coolvnod/palm-scan/hardware/kicad/buzzer.kicad_sch

## KiCad design hardware/kicad/buzzer.kicad_sch (2026-09-14)

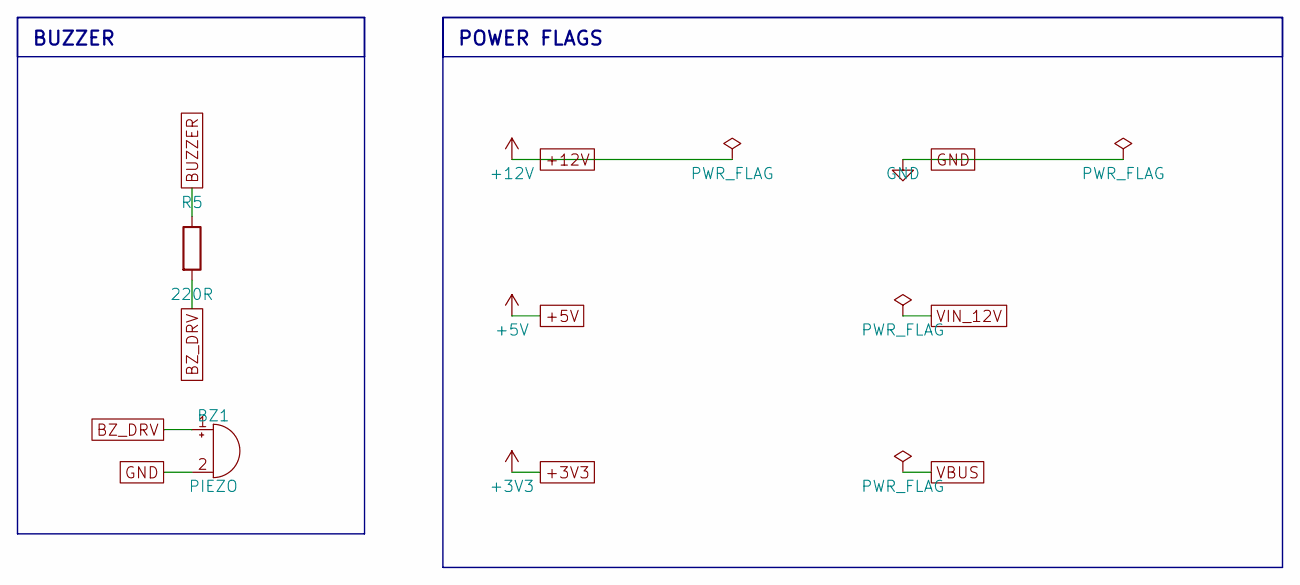
[picture p36: schematic buzzer.kicad_sch]

Parts:
BZ1: PIEZO; Buzzer_12x9.5RM7.6
R5: 220R; R_0603_1608Metric

Connections:
BUZZER: R5.1
BZ_DRV: BZ1.1 (+), R5.2
GND: BZ1.2 (-)

Notes on the sheet:
BUZZER
POWER FLAGS
