coolvnod/palm-scan/hardware/kicad/display.kicad_sch

## KiCad design hardware/kicad/display.kicad_sch (2026-09-14)

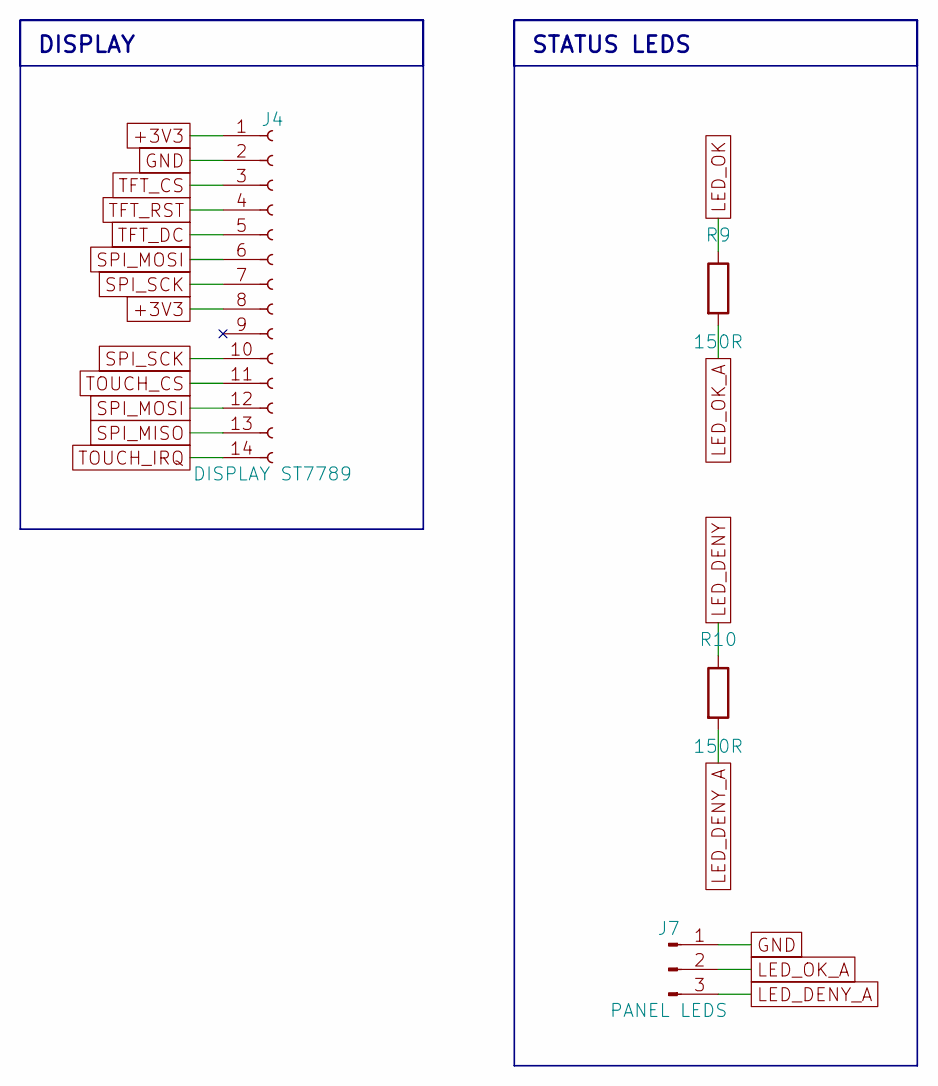
[picture p37: schematic display.kicad_sch]

Parts:
J4: DISPLAY ST7789; PinSocket_1x14_P2.54mm_Vertical
J7: PANEL LEDS; PinHeader_1x03_P2.54mm_Vertical
R9, R10: 150R; R_0603_1608Metric

Connections:
+3V3: J4.1, J4.8
GND: J4.2, J7.1
LED_DENY: R10.1
LED_DENY_A: J7.3, R10.2
LED_OK: R9.1
LED_OK_A: J7.2, R9.2
SPI_MISO: J4.13
SPI_MOSI: J4.6, J4.12
SPI_SCK: J4.7, J4.10
TFT_CS: J4.3
TFT_DC: J4.5
TFT_RST: J4.4
TOUCH_CS: J4.11
TOUCH_IRQ: J4.14

Notes on the sheet:
DISPLAY
STATUS LEDS
