coolvnod/palm-scan/hardware/kicad/exit.kicad_sch

## KiCad design hardware/kicad/exit.kicad_sch (2026-09-14)

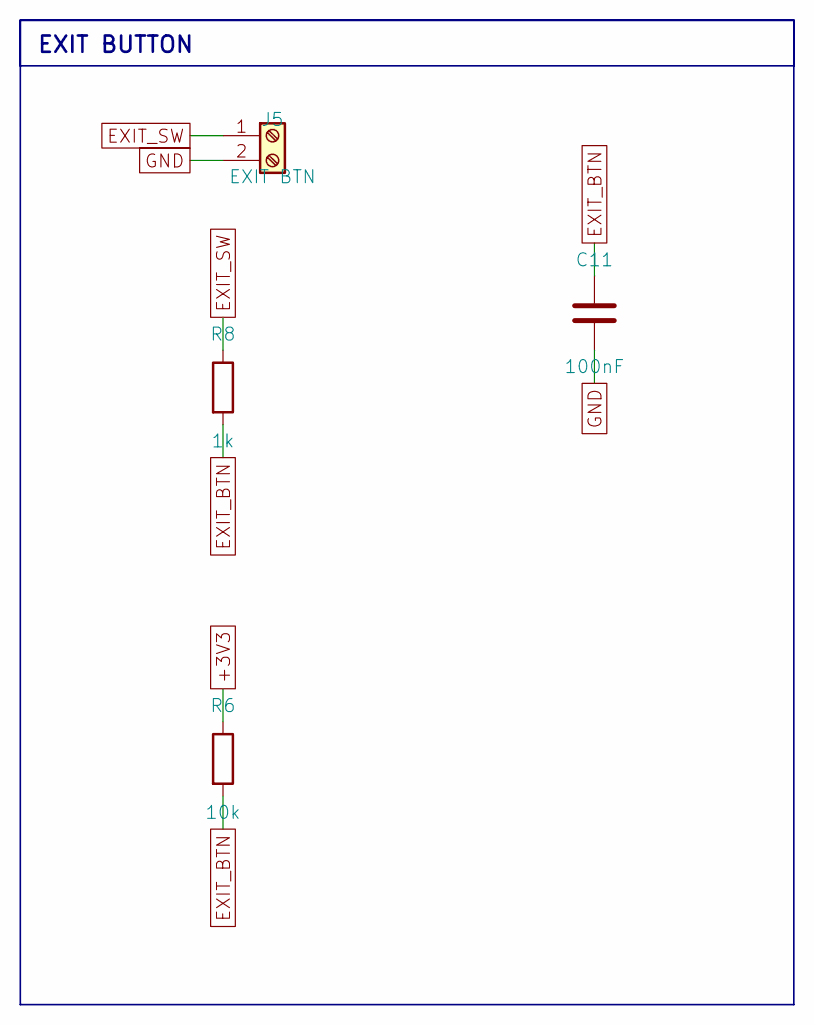
[picture p38: schematic exit.kicad_sch]

Parts:
C11: 100nF; C_0603_1608Metric
J5: EXIT BTN; TerminalBlock_Phoenix_MKDS-1,5-2-5.08_1x02_P5.08mm_Horizont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
R6: 10k; R_0603_1608Metric
R8: 1k; R_0603_1608Metric

Connections:
+3V3: R6.1
EXIT_BTN: C11.1, R6.2, R8.2
EXIT_SW: J5.1, R8.1
GND: C11.2, J5.2

Notes on the sheet:
EXIT BUTTON
