coolvnod/palm-scan/hardware/kicad/lock.kicad_sch

## KiCad design hardware/kicad/lock.kicad_sch (2026-09-14)

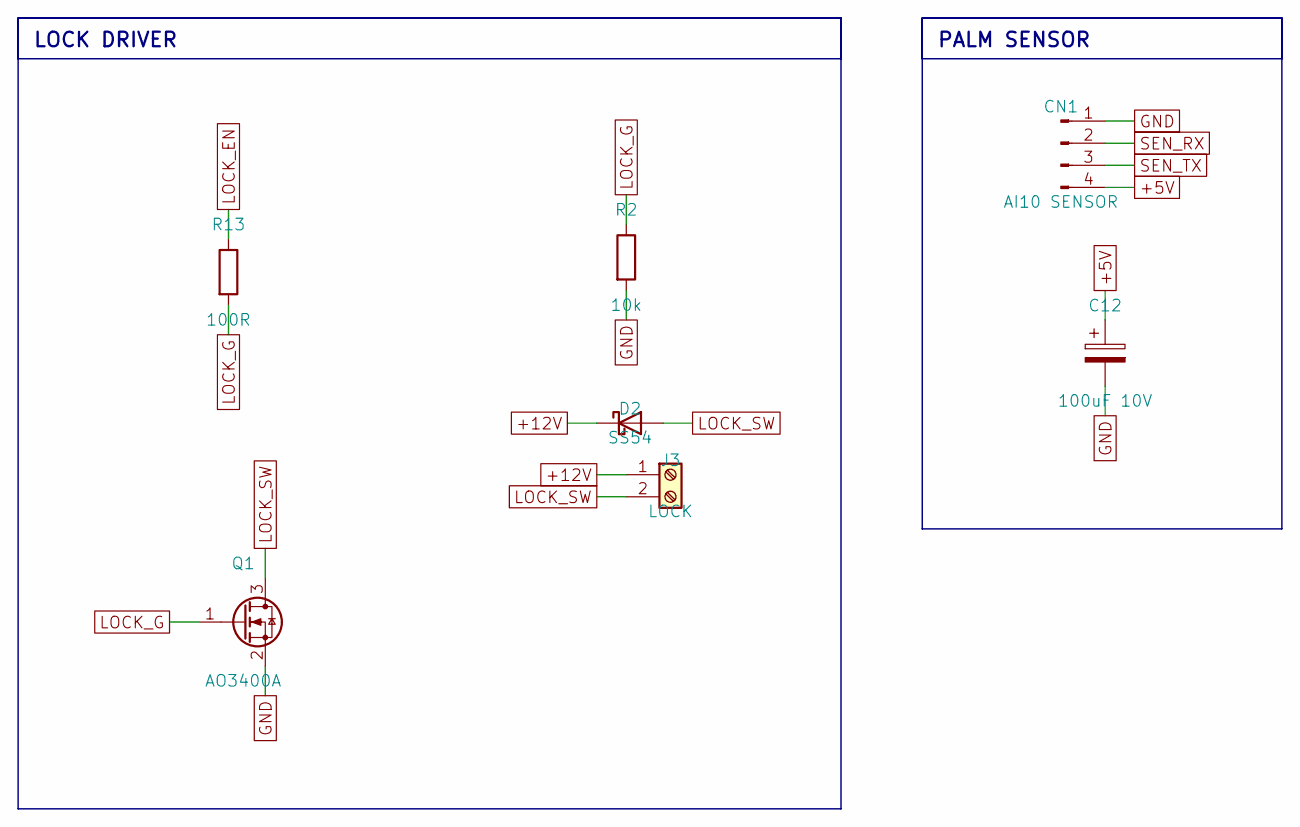
[picture p39: schematic lock.kicad_sch]

Parts:
C12: 100uF 10V; CP_Elec_6.3x5.4
CN1: AI10 SENSOR; Molex_PicoBlade_53047-0410_1x04_P1.25mm_Vertical
D2: SS54; D_SMA
J3: LOCK; TerminalBlock_Phoenix_MKDS-1,5-2-5.08_1x02_P5.08mm_Horizont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
Q1: AO3400A; SOT-23
R2: 10k; R_0603_1608Metric
R13: 100R; R_0603_1608Metric

Connections:
+5V: C12.1, CN1.4
+12V: D2.1 (K), J3.1
GND: C12.2, CN1.1, Q1.2 (S), R2.2
LOCK_EN: R13.1
LOCK_G: Q1.1 (G), R2.1, R13.2
LOCK_SW: D2.2 (A), J3.2, Q1.3 (D)
SEN_RX: CN1.2
SEN_TX: CN1.3

Notes on the sheet:
LOCK DRIVER
PALM SENSOR
