coolvnod/palm-scan/hardware/kicad/mcu.kicad_sch

## KiCad design hardware/kicad/mcu.kicad_sch (2026-09-14)

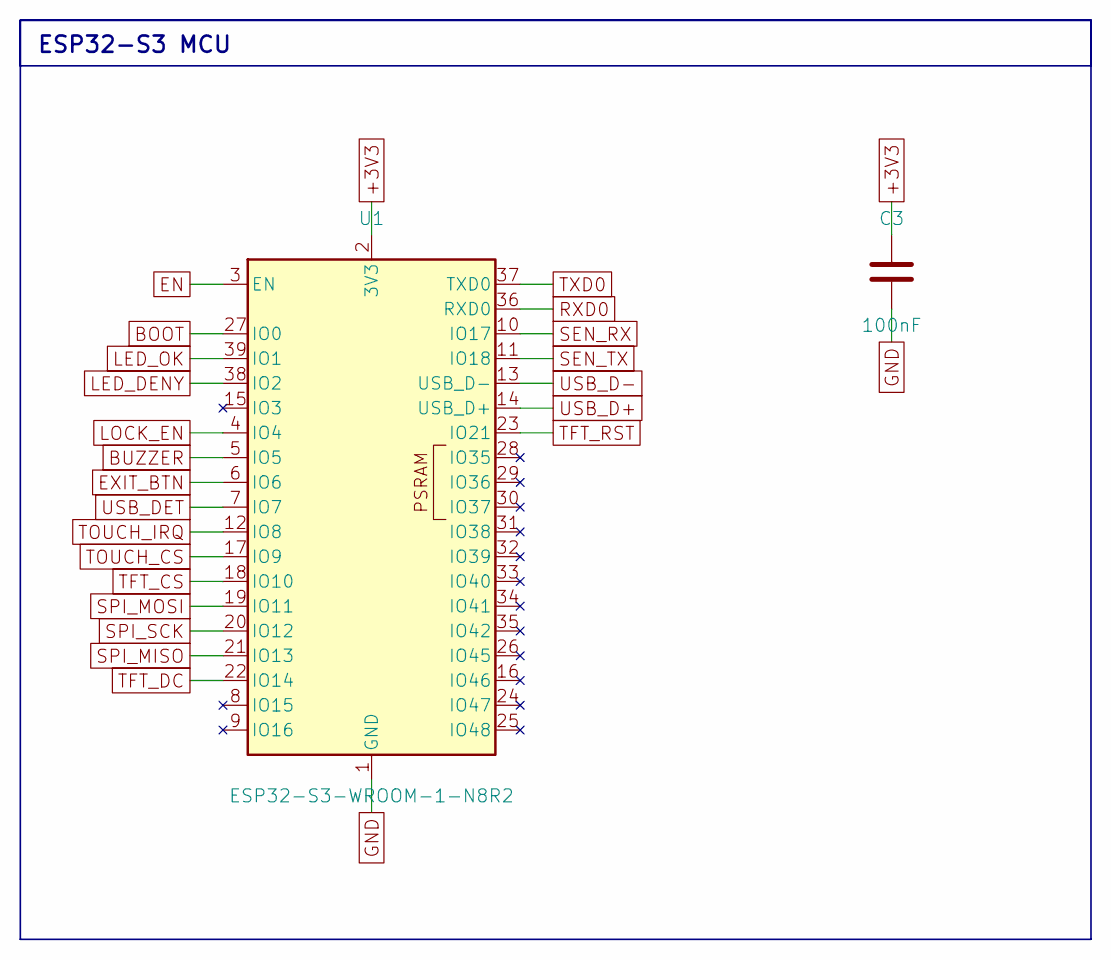
[picture p40: schematic mcu.kicad_sch]

Parts:
C3: 100nF; C_0603_1608Metric
U1: ESP32-S3-WROOM-1-N8R2; ESP32-S3-WROOM-1

Connections:
+3V3: C3.1, U1.2 (3V3)
BOOT: U1.27 (IO0)
BUZZER: U1.5 (IO5)
EN: U1.3 (EN)
EXIT_BTN: U1.6 (IO6)
GND: C3.2, U1.1 (GND), U1.40 (GND), U1.41 (GND)
LED_DENY: U1.38 (IO2)
LED_OK: U1.39 (IO1)
LOCK_EN: U1.4 (IO4)
RXD0: U1.36 (RXD0)
SEN_RX: U1.10 (IO17)
SEN_TX: U1.11 (IO18)
SPI_MISO: U1.21 (IO13)
SPI_MOSI: U1.19 (IO11)
SPI_SCK: U1.20 (IO12)
TFT_CS: U1.18 (IO10)
TFT_DC: U1.22 (IO14)
TFT_RST: U1.23 (IO21)
TOUCH_CS: U1.17 (IO9)
TOUCH_IRQ: U1.12 (IO8)
TXD0: U1.37 (TXD0)
USB_D+: U1.14 (USB_D+)
USB_D-: U1.13 (USB_D-)
USB_DET: U1.7 (IO7)

Notes on the sheet:
ESP32-S3 MCU
