coolvnod/palm-scan/hardware/kicad/power_in.kicad_sch

## KiCad design hardware/kicad/power_in.kicad_sch (2026-09-14)

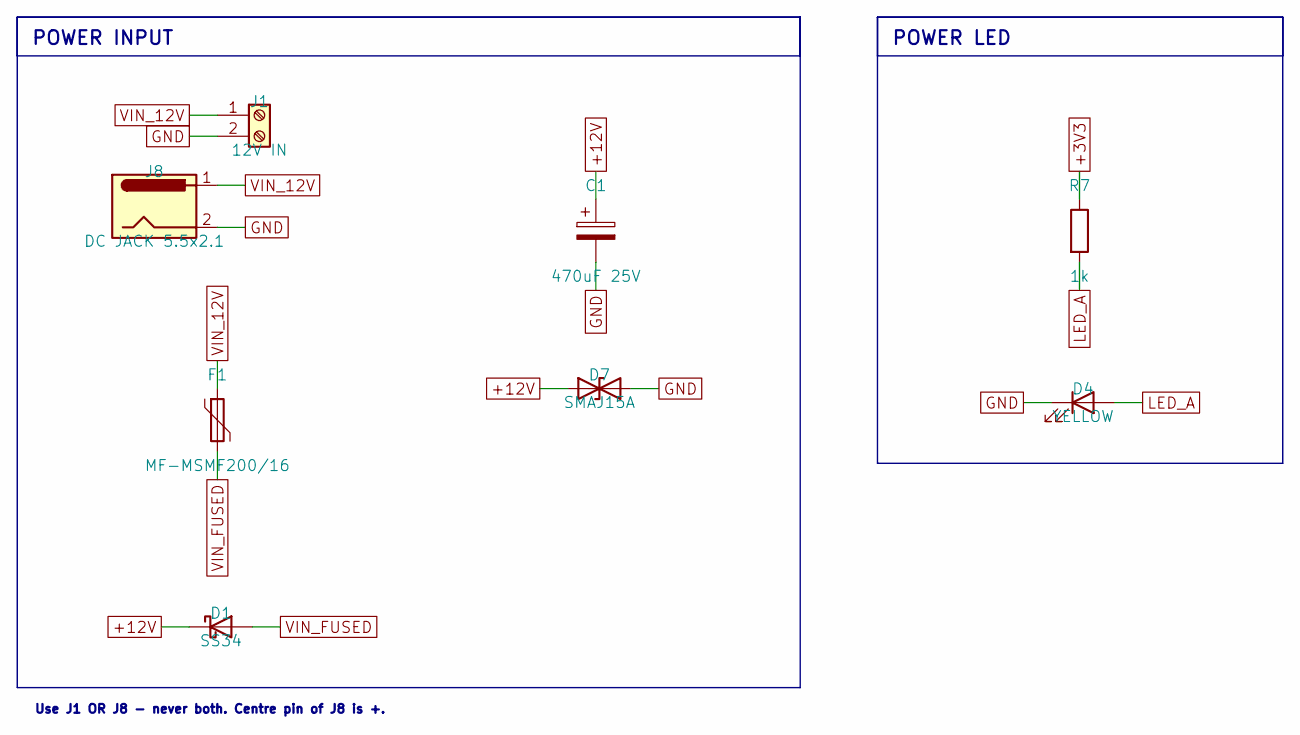
[picture p41: schematic power_in.kicad_sch]

Parts:
C1: 470uF 25V; CP_Radial_D8.0mm_P3.50mm
D1: SS34; D_SMA
D4: YELLOW; LED_0603_1608Metric
D7: SMAJ15A; D_SMA
F1: MF-MSMF200/16; Fuse_1812_4532Metric
J1: 12V IN; TerminalBlock_Phoenix_MKDS-1,5-2-5.08_1x02_P5.08mm_Horizont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
J8: DC JACK 5.5x2.1; BarrelJack_Horizontal
R7: 1k; R_0603_1608Metric

Connections:
+3V3: R7.1
+12V: C1.1, D1.1 (K), D7.1 (A1)
GND: C1.2, D4.1 (K), D7.2 (A2), J1.2, J8.2
LED_A: D4.2 (A), R7.2
VIN_12V: F1.1, J1.1, J8.1
VIN_FUSED: D1.2 (A), F1.2

Notes on the sheet:
POWER INPUT
Use J1 OR J8 - never both. Centre pin of J8 is +.
POWER LED
