coolvnod/palm-scan/hardware/kicad/power_reg.kicad_sch

## KiCad design hardware/kicad/power_reg.kicad_sch (2026-09-14)

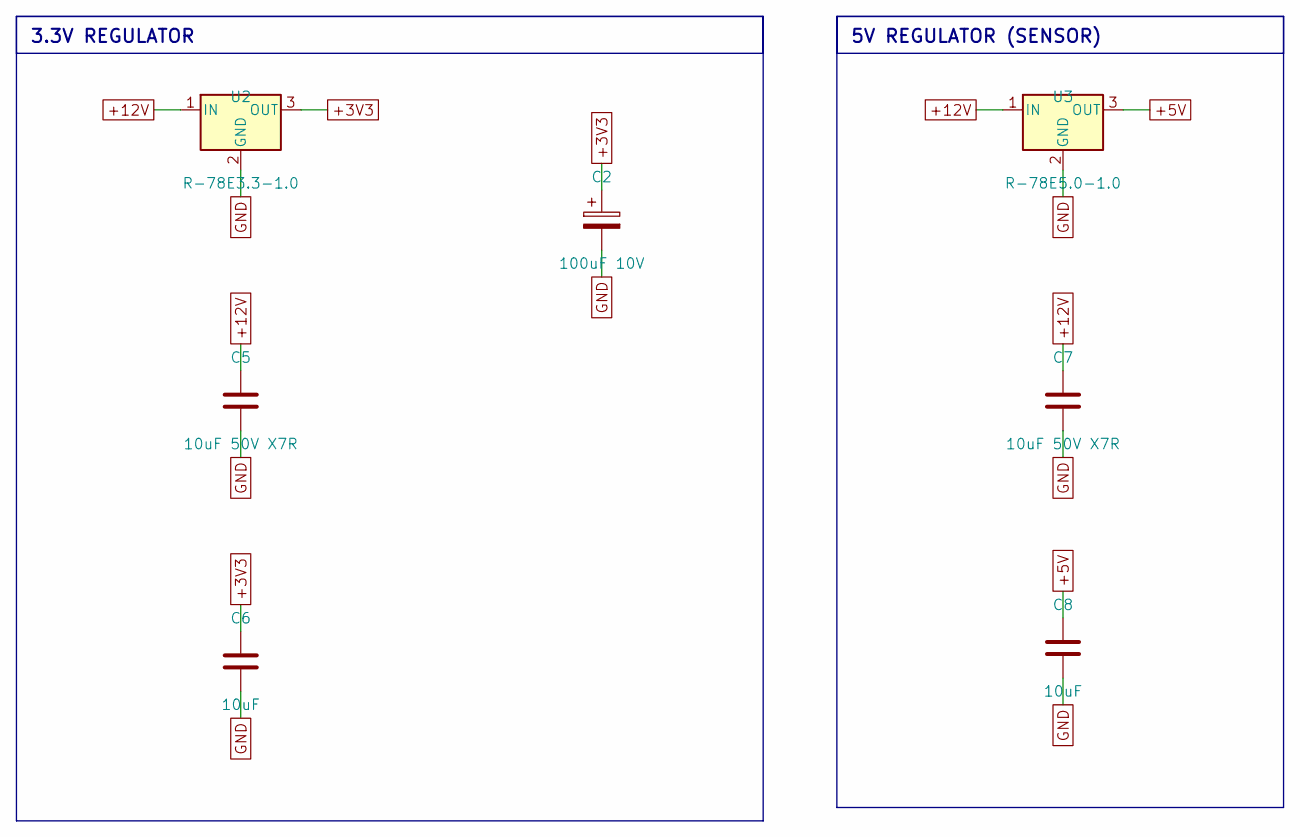
[picture p42: schematic power_reg.kicad_sch]

Parts:
C2: 100uF 10V; CP_Elec_6.3x5.4
C5, C7: 10uF 50V X7R; C_1210_3225Metric
C6, C8: 10uF; C_0805_2012Metric
U2: R-78E3.3-1.0; Converter_DCDC_RECOM_R-78E-0.5_THT
U3: R-78E5.0-1.0; Converter_DCDC_RECOM_R-78E-0.5_THT

Connections:
+3V3: C2.1, C6.1, U2.3 (OUT)
+5V: C8.1, U3.3 (OUT)
+12V: C5.1, C7.1, U2.1 (IN), U3.1 (IN)
GND: C2.2, C5.2, C6.2, C7.2, C8.2, U2.2 (GND), U3.2 (GND)

Notes on the sheet:
3.3V REGULATOR
5V REGULATOR (SENSOR)
