coolvnod/palm-scan/hardware/kicad/reset_boot.kicad_sch

## KiCad design hardware/kicad/reset_boot.kicad_sch (2026-09-14)

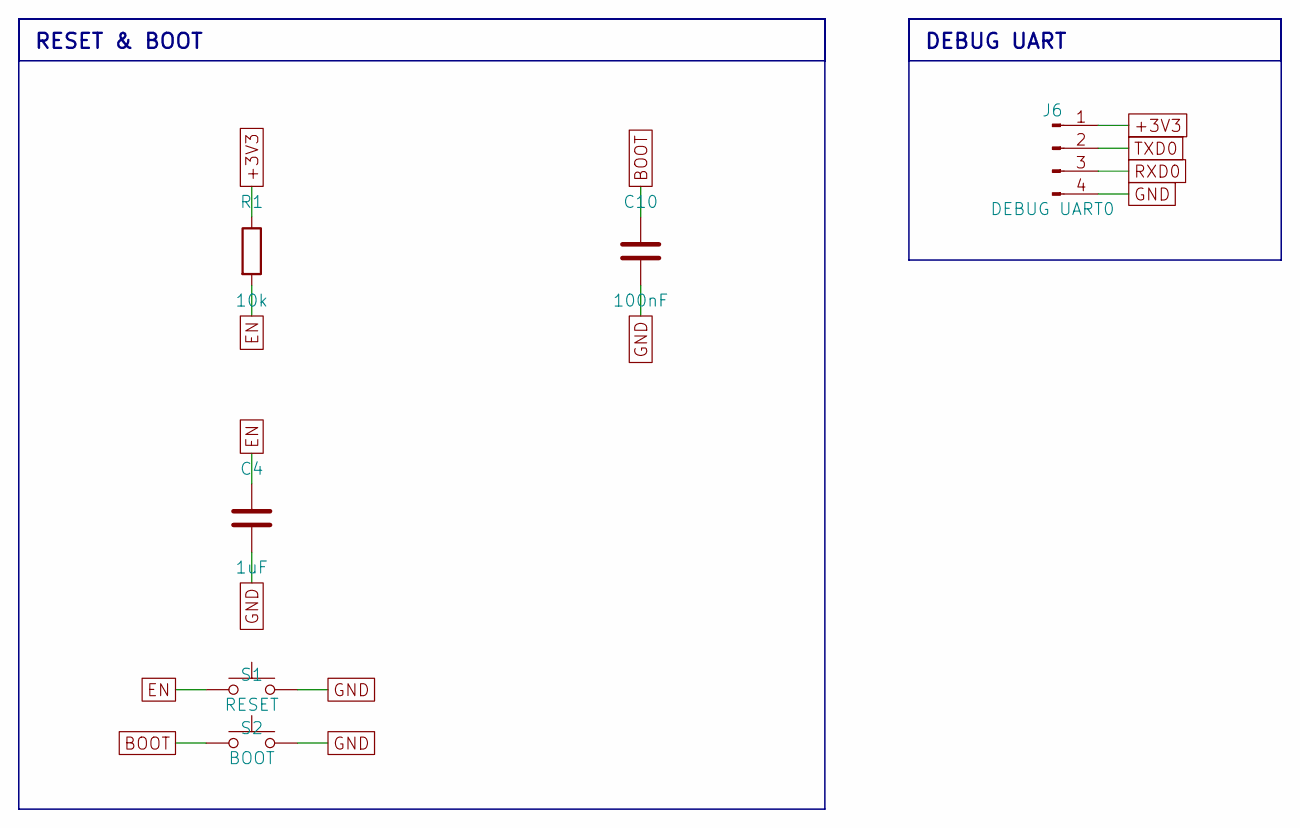
[picture p43: schematic reset_boot.kicad_sch]

Parts:
C4: 1uF; C_0603_1608Metric
C10: 100nF; C_0603_1608Metric
J6: DEBUG UART0; PinHeader_1x04_P2.54mm_Vertical
R1: 10k; R_0603_1608Metric
S1: RESET; SW_Push_1P1T_NO_CK_KMR2
S2: BOOT; SW_Push_1P1T_NO_CK_KMR2

Connections:
+3V3: J6.1, R1.1
BOOT: C10.1, S2.1
EN: C4.1, R1.2, S1.1
GND: C4.2, C10.2, J6.4, S1.2, S2.2
RXD0: J6.3
TXD0: J6.2

Notes on the sheet:
RESET & BOOT
DEBUG UART
