coolvnod/palm-scan/hardware/kicad/usb.kicad_sch

## KiCad design hardware/kicad/usb.kicad_sch (2026-09-14)

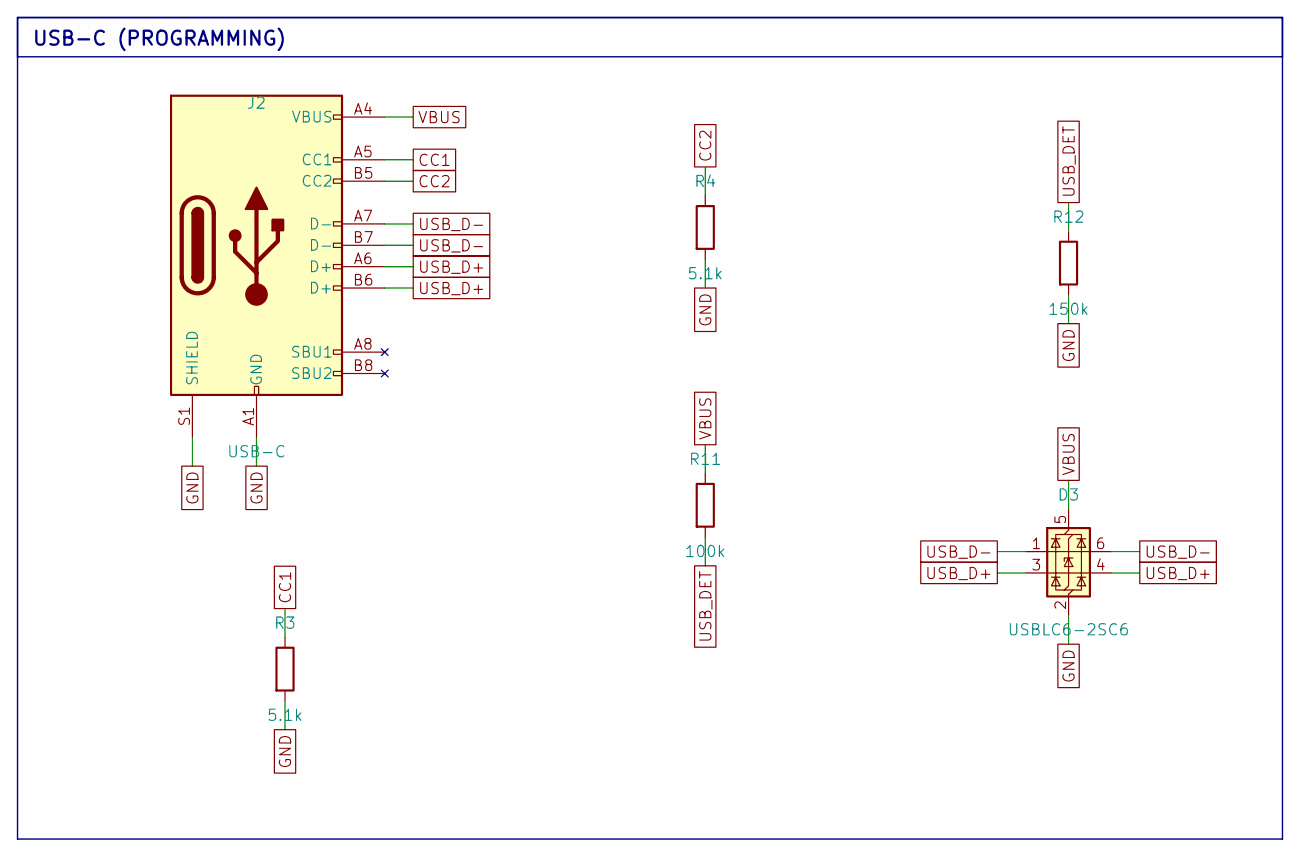
[picture p44: schematic usb.kicad_sch]

Parts:
D3: USBLC6-2SC6; SOT-23-6
J2: USB-C; USB_C_Receptacle_HRO_TYPE-C-31-M-12
R3, R4: 5.1k; R_0603_1608Metric
R11: 100k; R_0603_1608Metric
R12: 150k; R_0603_1608Metric

Connections:
CC1: J2.A5 (CC1), R3.1
CC2: J2.B5 (CC2), R4.1
GND: D3.2 (GND), J2.A1 (GND), J2.A12 (GND), J2.B1 (GND), J2.B12 (GND), J2.S1 (SHIELD), R3.2, R4.2, R12.2
USB_D+: D3.3 (I/O2), D3.4 (I/O2), J2.A6 (D+), J2.B6 (D+)
USB_D-: D3.1 (I/O1), D3.6 (I/O1), J2.A7 (D-), J2.B7 (D-)
USB_DET: R11.2, R12.1
VBUS: D3.5 (VBUS), J2.A4 (VBUS), J2.A9 (VBUS), J2.B4 (VBUS), J2.B9 (VBUS), R11.1

Notes on the sheet:
USB-C (PROGRAMMING)
